ItamarIliuk/Bumper-Bot/bumperbot_description/photos/DeskPortraitA_01.jpg

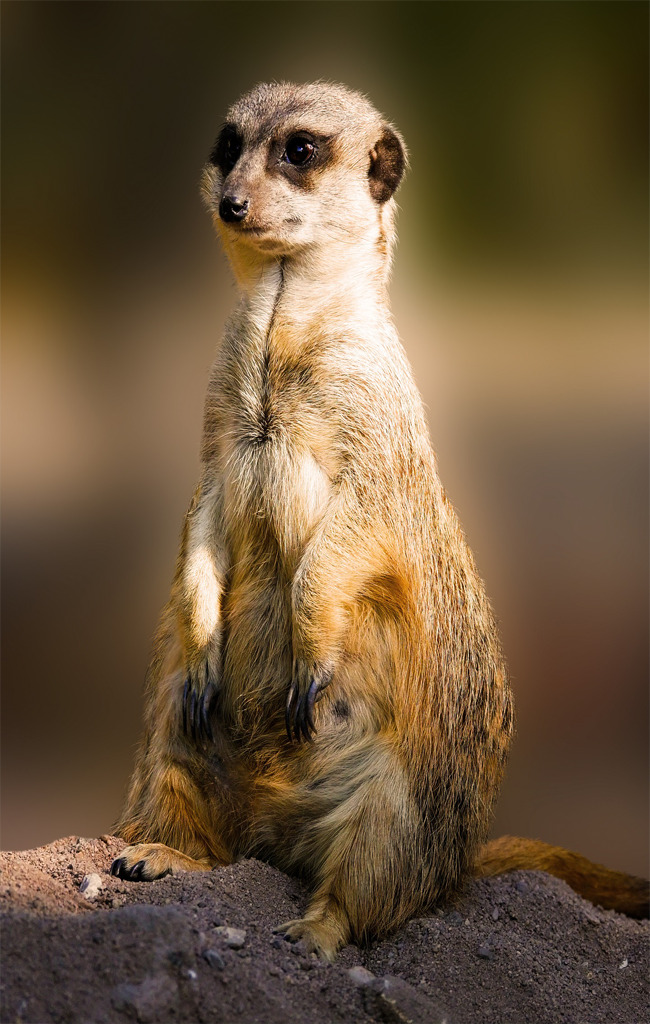
bumperbot_description/photos/DeskPortraitA_01.jpg
