ItamarIliuk/Bumper-Bot/bumperbot_description/photos/DeskPortraitA_02.jpg

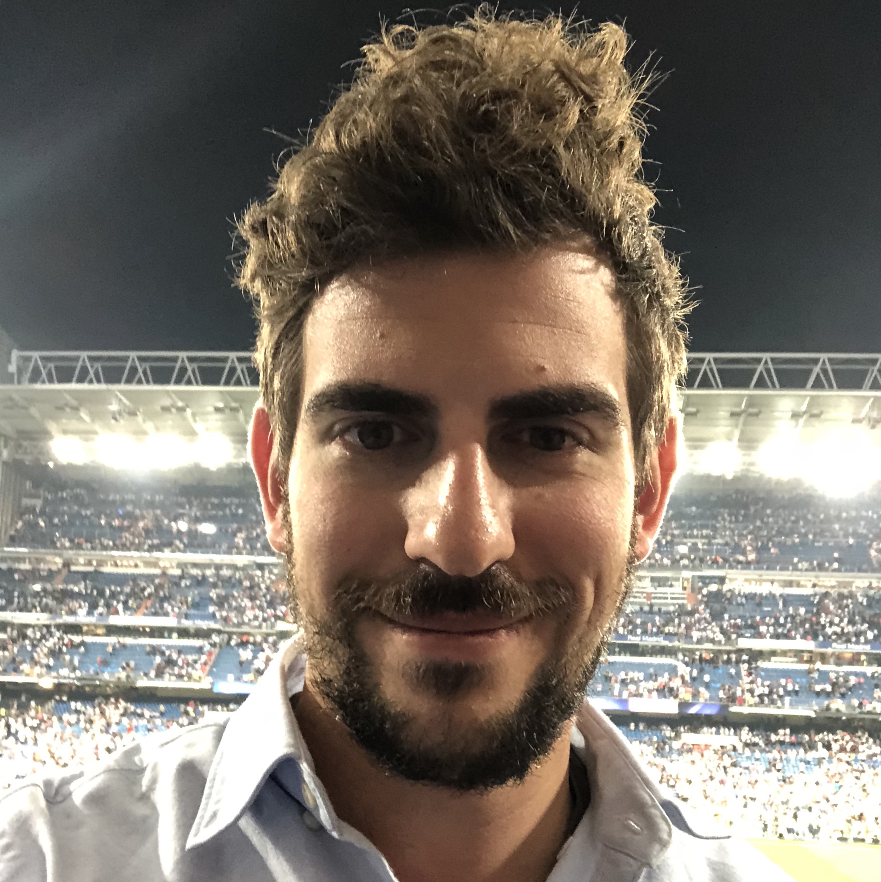
bumperbot_description/photos/DeskPortraitA_02.jpg
