ItamarIliuk/Bumper-Bot/bumperbot_description/photos/DeskPortraitB_01.jpg

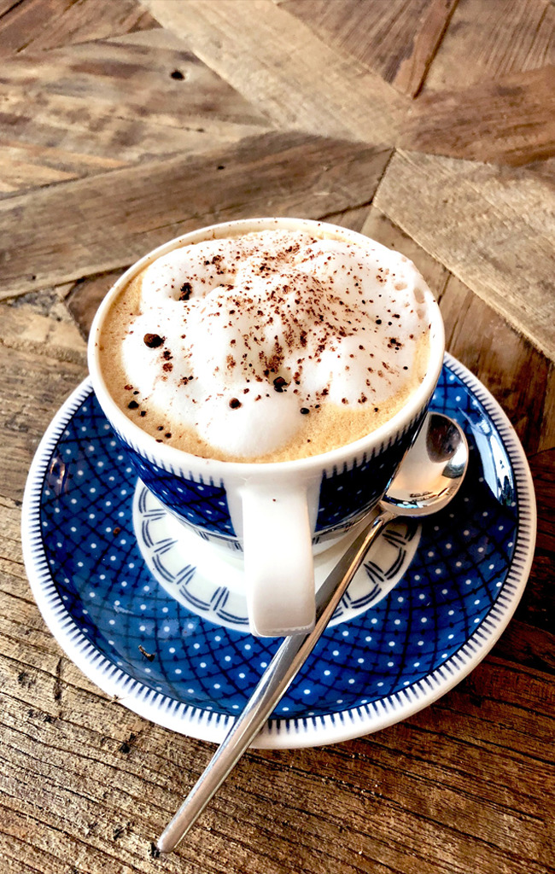
bumperbot_description/photos/DeskPortraitB_01.jpg
