ItamarIliuk/Bumper-Bot/bumperbot_description/photos/DeskPortraitC_02.jpg

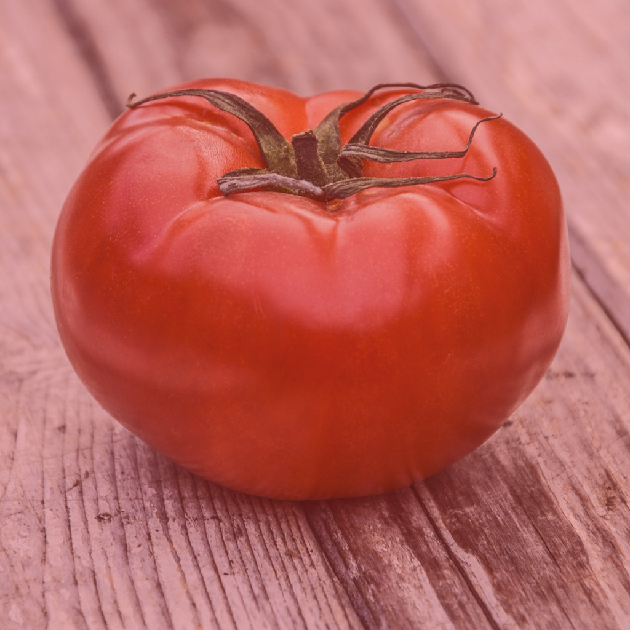
bumperbot_description/photos/DeskPortraitC_02.jpg
