ItamarIliuk/Bumper-Bot/bumperbot_description/photos/DeskPortraitD_01.jpg

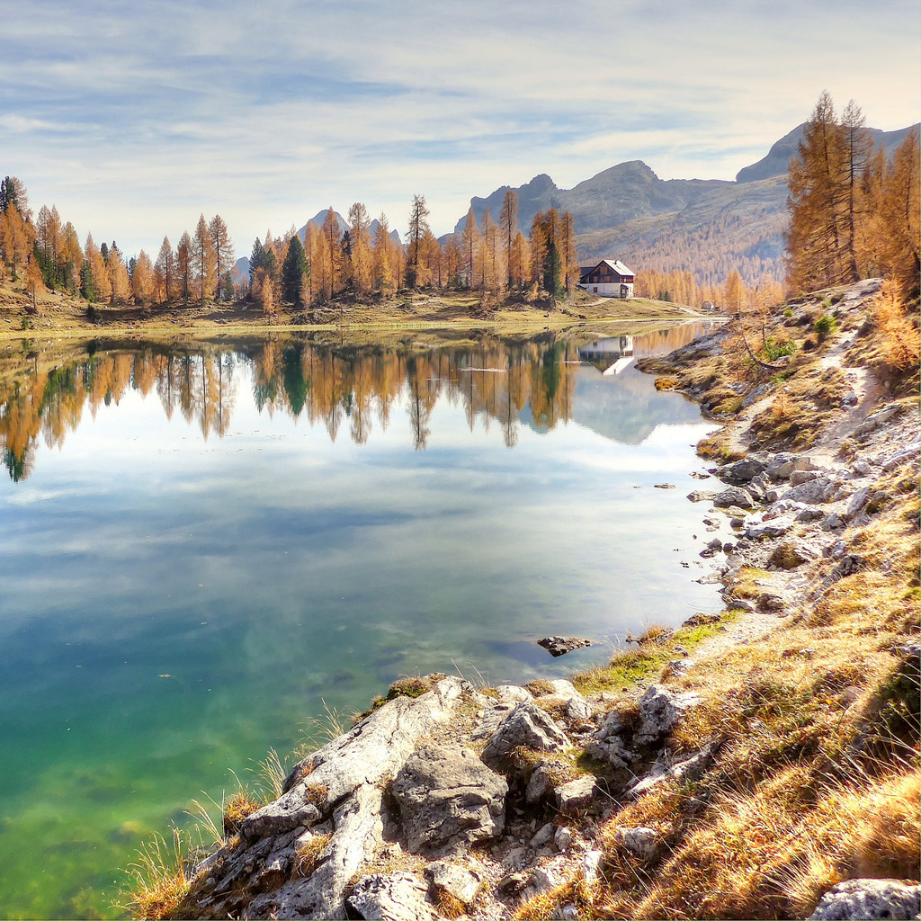
bumperbot_description/photos/DeskPortraitD_01.jpg
