ItamarIliuk/Bumper-Bot/bumperbot_description/photos/DeskPortraitD_04.jpg

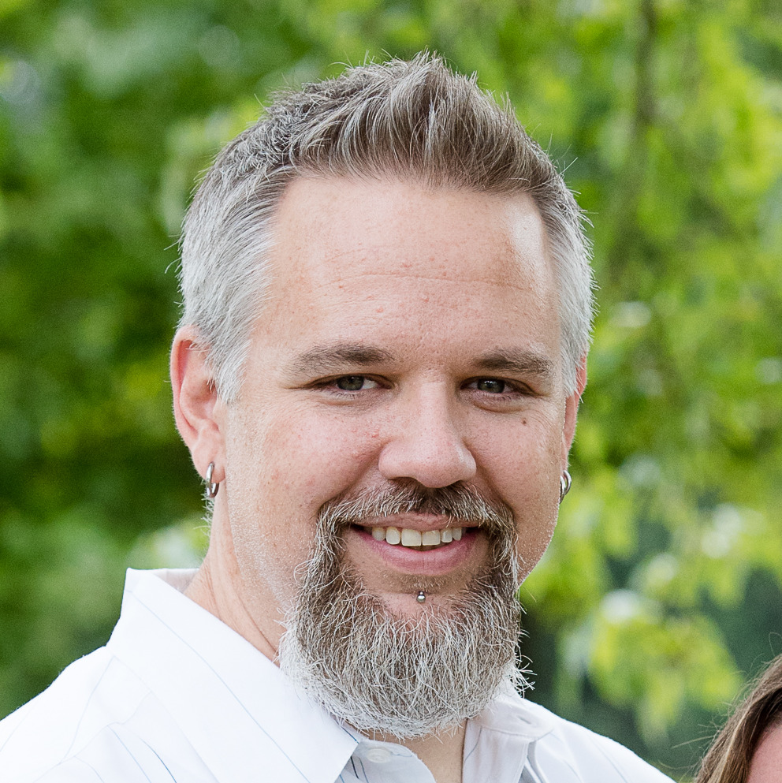
bumperbot_description/photos/DeskPortraitD_04.jpg
