ItamarIliuk/Bumper-Bot/bumperbot_description/photos/PortraitA_01.jpg

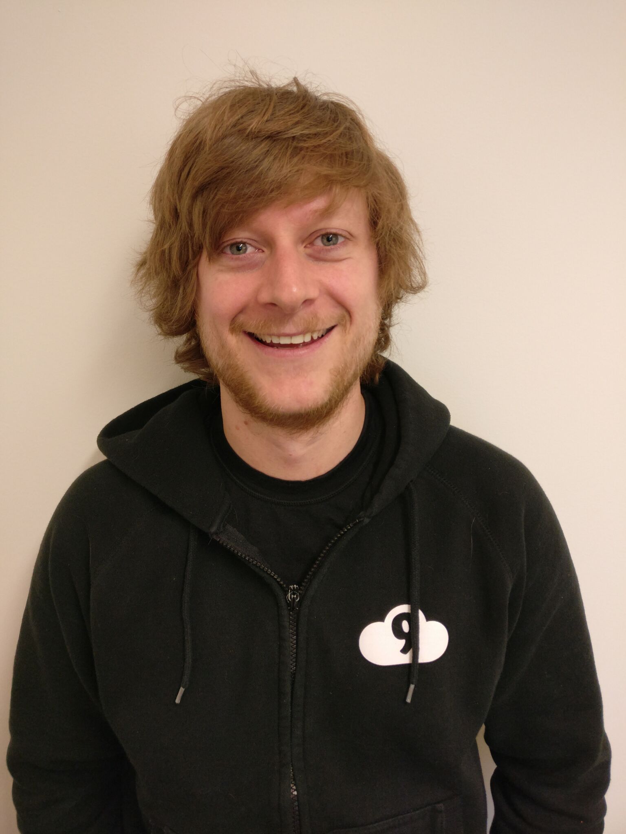
bumperbot_description/photos/PortraitA_01.jpg
