ItamarIliuk/Bumper-Bot/bumperbot_description/photos/PortraitA_02.jpg

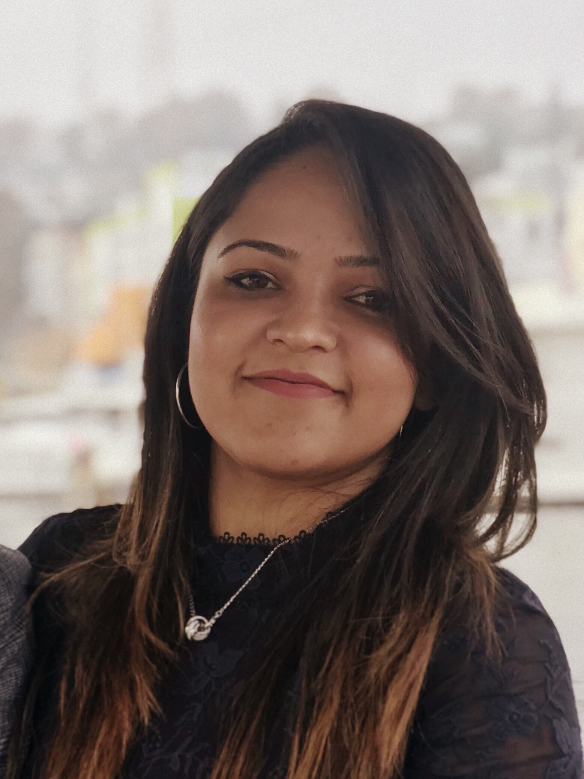
bumperbot_description/photos/PortraitA_02.jpg
