ItamarIliuk/Bumper-Bot/bumperbot_description/photos/PortraitB_01.jpg

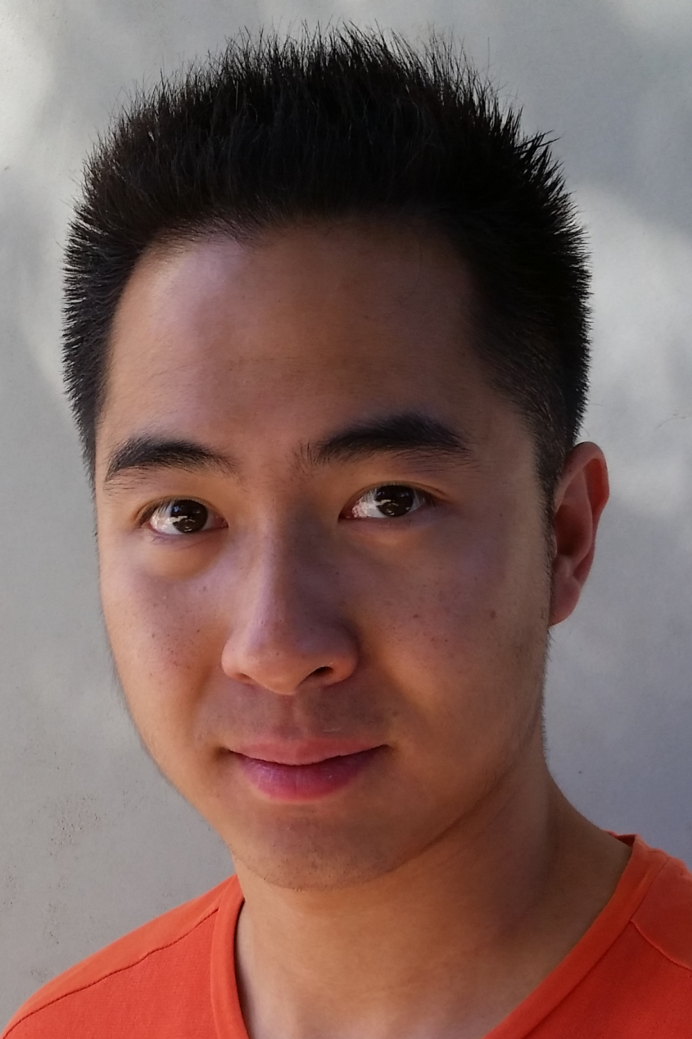
bumperbot_description/photos/PortraitB_01.jpg
