ItamarIliuk/Bumper-Bot/bumperbot_description/photos/PortraitB_02.jpg

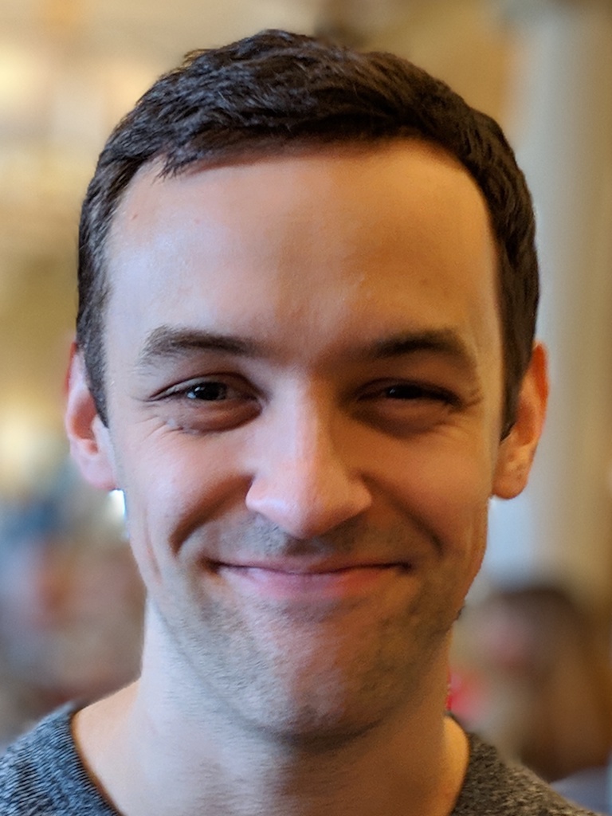
bumperbot_description/photos/PortraitB_02.jpg
