ItamarIliuk/Bumper-Bot/bumperbot_description/photos/PortraitB_03.jpg

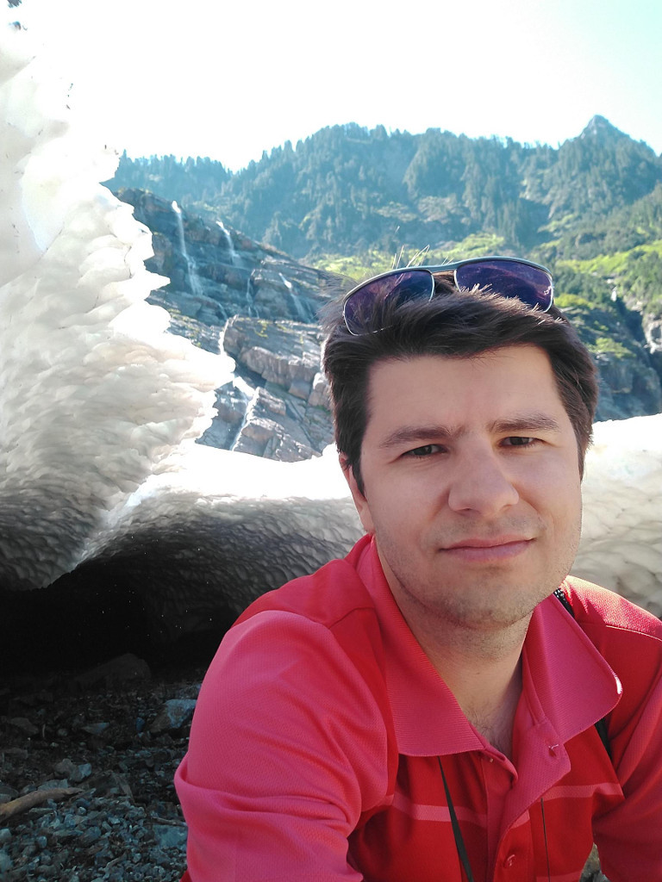
bumperbot_description/photos/PortraitB_03.jpg
