ItamarIliuk/Bumper-Bot/bumperbot_description/photos/PortraitC_01.jpg

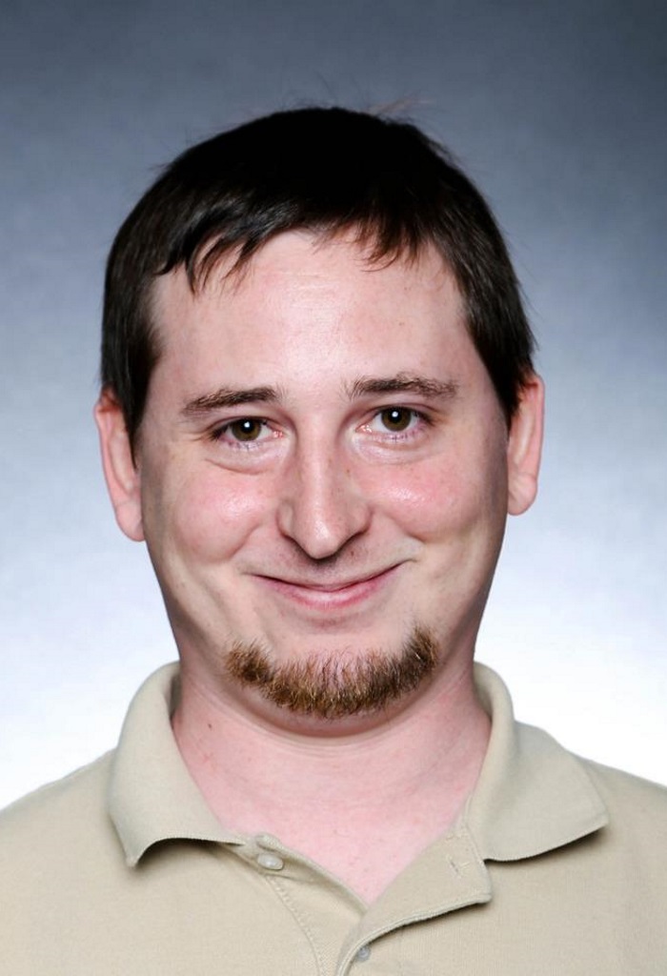
bumperbot_description/photos/PortraitC_01.jpg
