ItamarIliuk/Bumper-Bot/bumperbot_description/photos/PortraitD_01.jpg

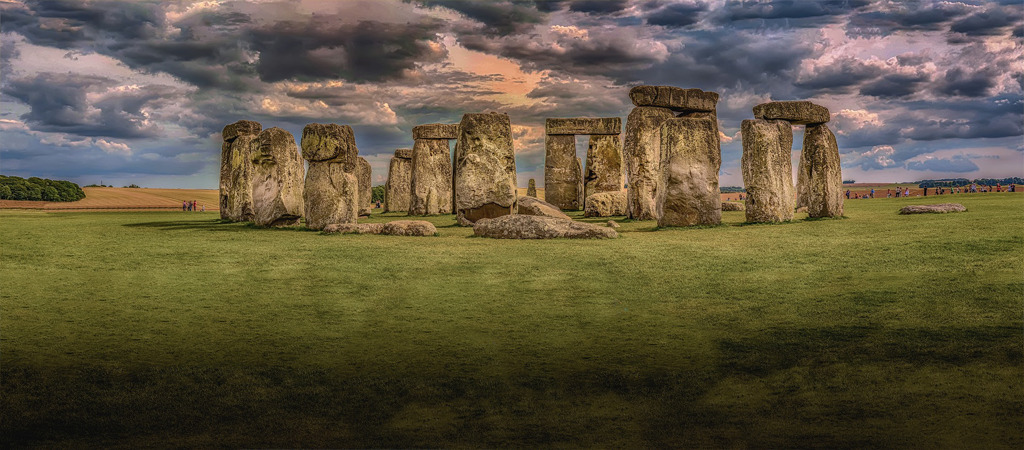
bumperbot_description/photos/PortraitD_01.jpg
