ItamarIliuk/Bumper-Bot/bumperbot_description/photos/PortraitE_01.jpg

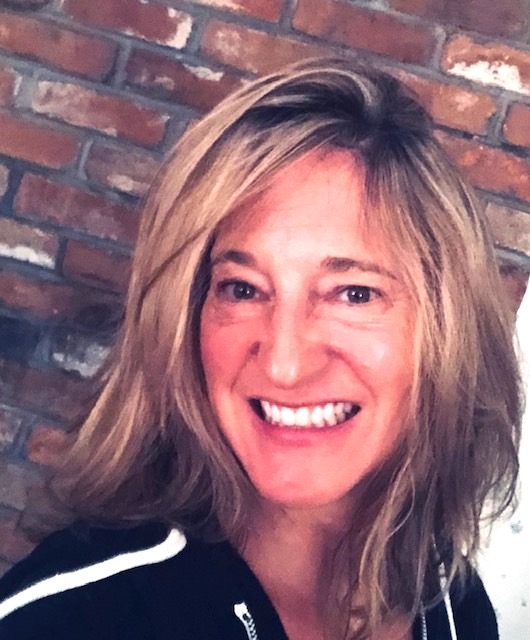
bumperbot_description/photos/PortraitE_01.jpg
