ItamarIliuk/Bumper-Bot/bumperbot_description/photos/PortraitE_02.jpg

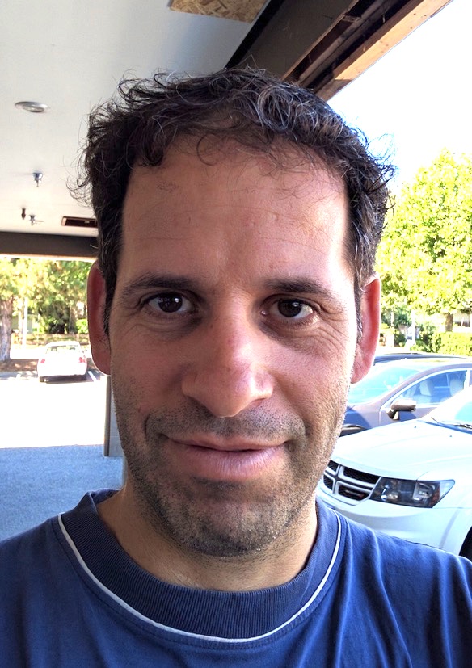
bumperbot_description/photos/PortraitE_02.jpg
