ItamarIliuk/Bumper-Bot/bumperbot_description/models/aws_robomaker_residential_Bed_01/materials/textures/aws_BedC_01.png

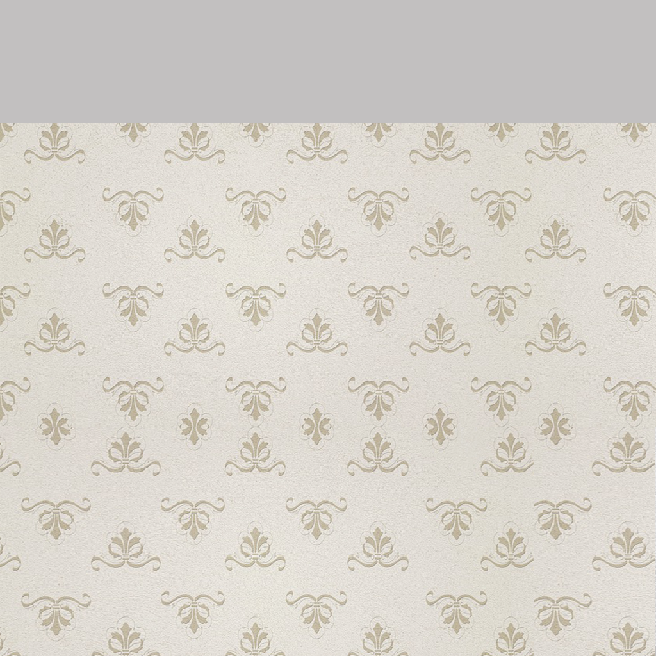
bumperbot_description/models/aws_robomaker_residential_Bed_01/materials/textures/aws_BedC_01.png
