ItamarIliuk/Bumper-Bot/bumperbot_description/models/aws_robomaker_residential_Board_01/materials/textures/aws_Board_01.png

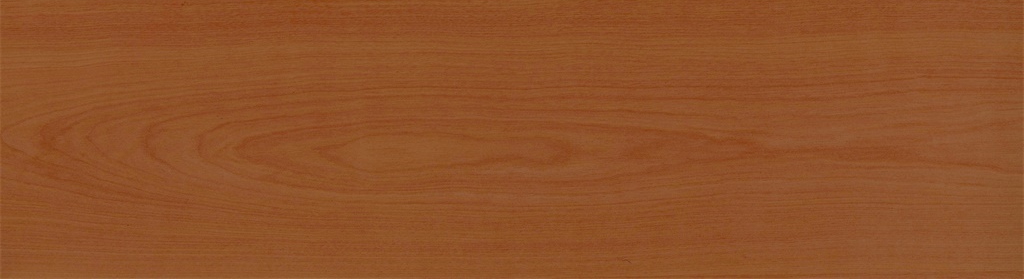
bumperbot_description/models/aws_robomaker_residential_Board_01/materials/textures/aws_Board_01.png
