ItamarIliuk/Bumper-Bot/bumperbot_description/models/aws_robomaker_residential_Door_01/materials/textures/aws_Door_01.png

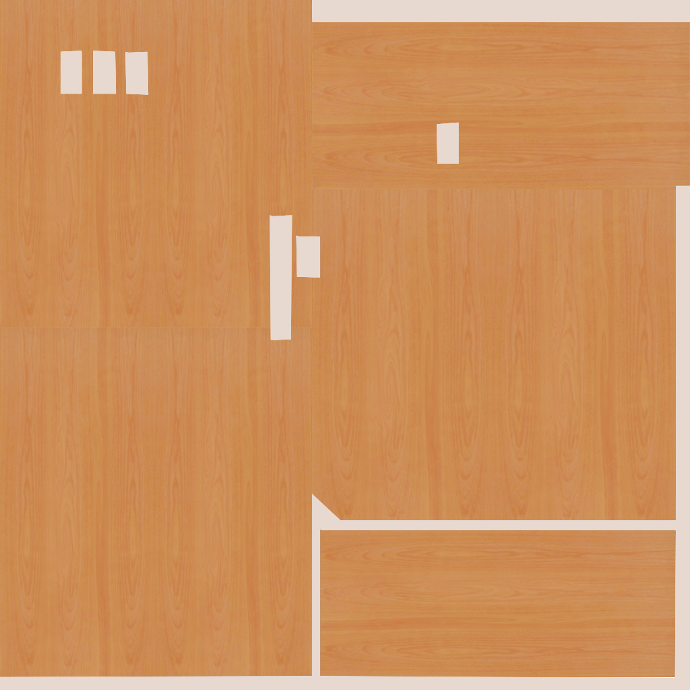
bumperbot_description/models/aws_robomaker_residential_Door_01/materials/textures/aws_Door_01.png
