ItamarIliuk/Bumper-Bot/bumperbot_description/models/aws_robomaker_residential_Handle_01/materials/textures/aws_Handle_01.png

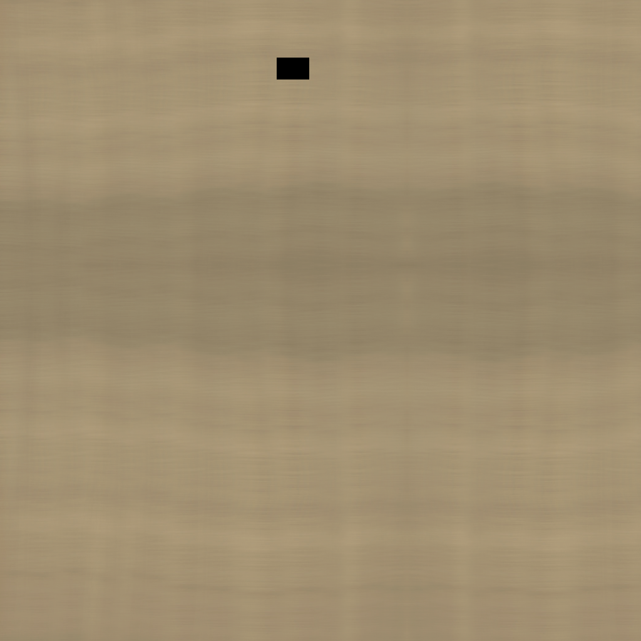
bumperbot_description/models/aws_robomaker_residential_Handle_01/materials/textures/aws_Handle_01.png
