ItamarIliuk/Bumper-Bot/bumperbot_description/models/aws_robomaker_residential_Trash_01/materials/textures/aws_Trash_01.png

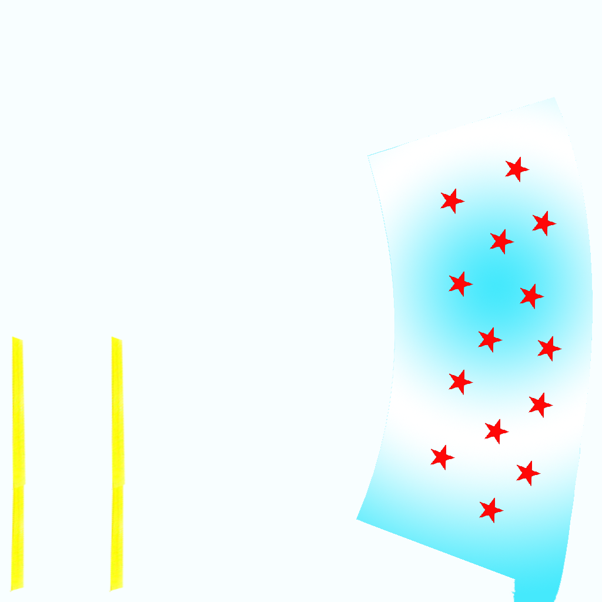
bumperbot_description/models/aws_robomaker_residential_Trash_01/materials/textures/aws_Trash_01.png
