ItamarIliuk/Bumper-Bot/bumperbot_description/models/aws_robomaker_residential_Vase_01/materials/textures/aws_Vase_01.png

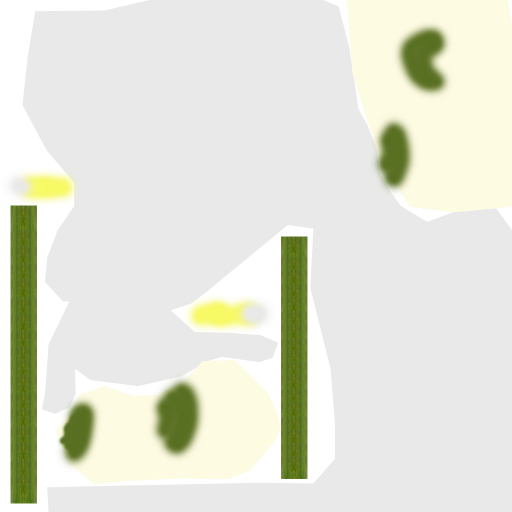
bumperbot_description/models/aws_robomaker_residential_Vase_01/materials/textures/aws_Vase_01.png
