ItamarIliuk/Bumper-Bot/bumperbot_hardware/CAD/TekniRoll.D30mm.TR670-001.SLDPRT

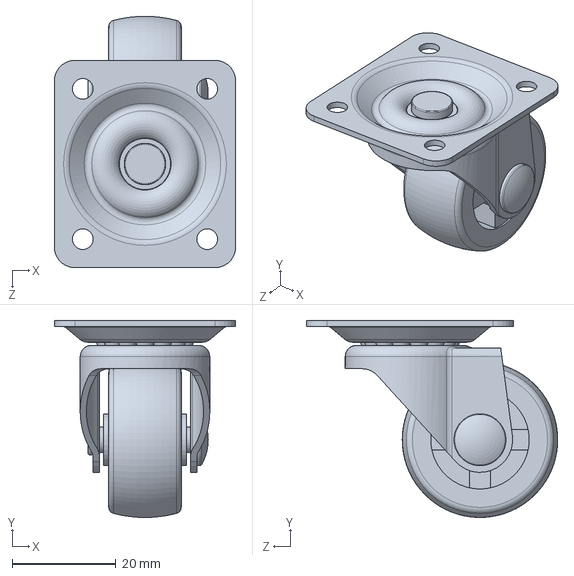
[picture p85: CAD file, 2024-10-19]
bumperbot_hardware/CAD/TekniRoll.D30mm.TR670-001.SLDPRT
35.0 x 38.0 x 48.5 mm
