ItamarIliuk/Bumper-Bot/bumperbot_hardware/CAD/battery_pack.SLDPRT

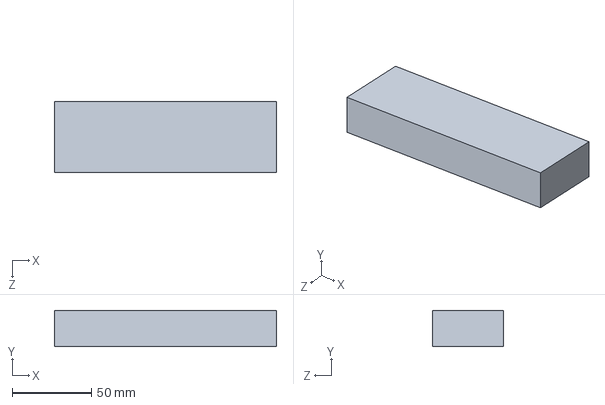
[picture p86: CAD file, 2024-10-19]
bumperbot_hardware/CAD/battery_pack.SLDPRT
140.0 x 23.0 x 45.0 mm
